LORDSn1per/OpenRemote-Hardware/PCB/Dock Rev6/Dock Rev6 3D Preview.png

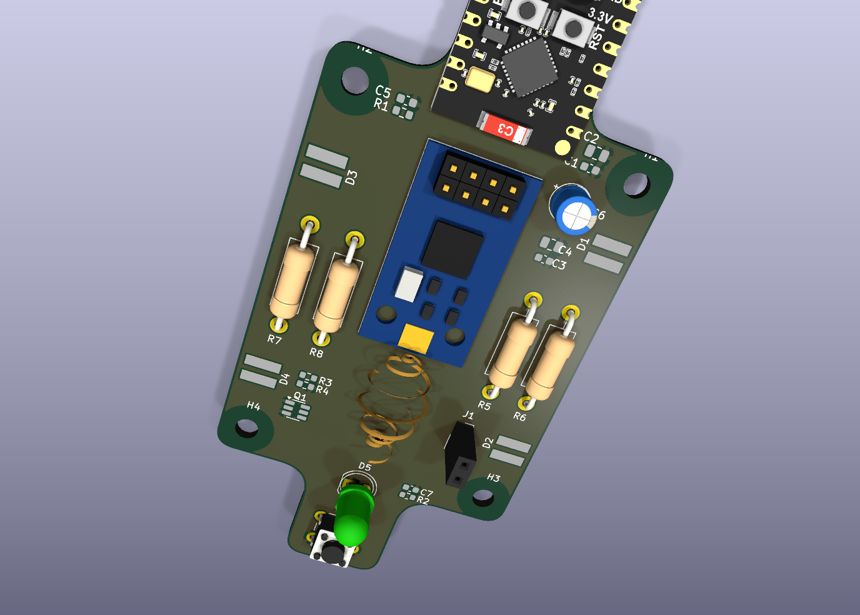
PCB/Dock Rev6/Dock Rev6 3D Preview.png
