LORDSn1per/OpenRemote-Hardware/CAD/Adafruit LCD/STL/Off Button Adafruit Rev6-v37.stl

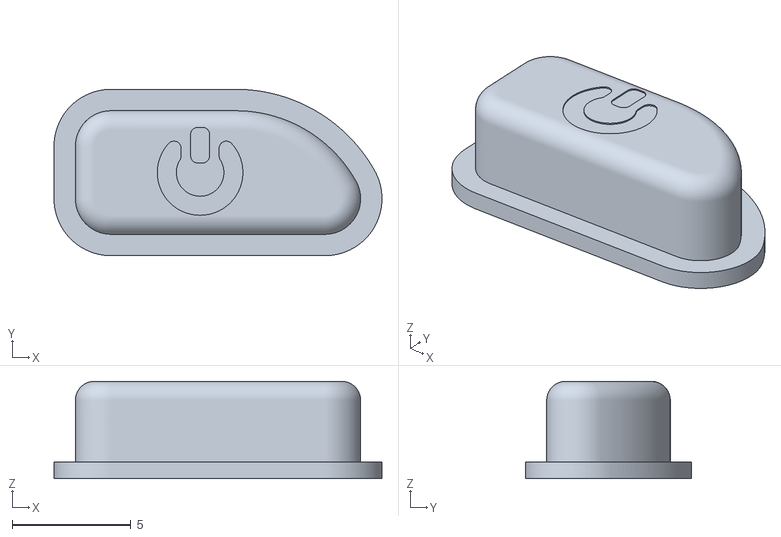
[picture p24: CAD file, 2026-09-03]
CAD/Adafruit LCD/STL/Off Button Adafruit Rev6-v37.stl
13.8 x 7.00 x 4.10
