LORDSn1per/OpenRemote-Hardware/CAD/BuyDisplay LCD/STL/Off Button BuyDisplay Rev6-v37.stl

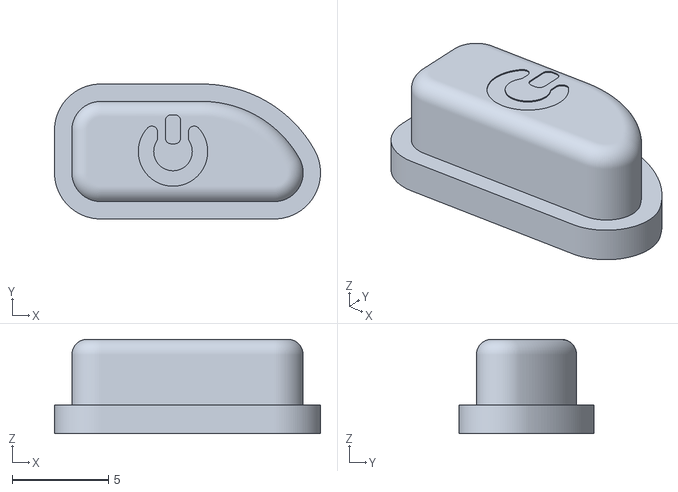
[picture p25: CAD file, 2026-09-03]
CAD/BuyDisplay LCD/STL/Off Button BuyDisplay Rev6-v37.stl
13.8 x 7.00 x 4.90
