LORDSn1per/OpenRemote-Hardware/CAD/Dock/STL/Dock Menu Button Rev6-v47.stl

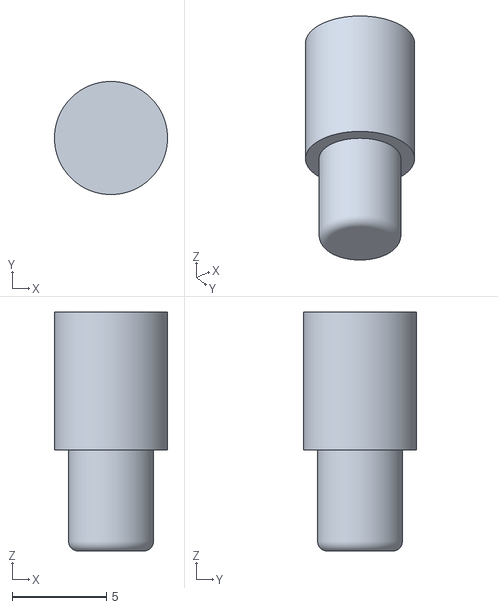
[picture p26: CAD file, 2026-09-03]
CAD/Dock/STL/Dock Menu Button Rev6-v47.stl
6.00 x 6.00 x 12.7
