LORDSn1per/OpenRemote-Hardware/PCB/Dock Rev6/project_libraries/3D-models/JST_Compatible_Female_1x02_P2.54mm.step

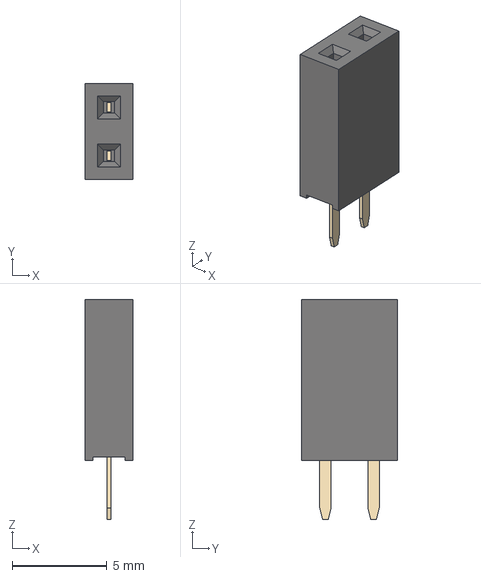
[picture p27: CAD file, 2026-08-27]
PCB/Dock Rev6/project_libraries/3D-models/JST_Compatible_Female_1x02_P2.54mm.step
2.54 x 5.08 x 11.6 mm
