LORDSn1per/OpenRemote-Hardware/PCB/Revision 6/project_libraries/3D-models/ER-TFT028-4.2_Folded.step

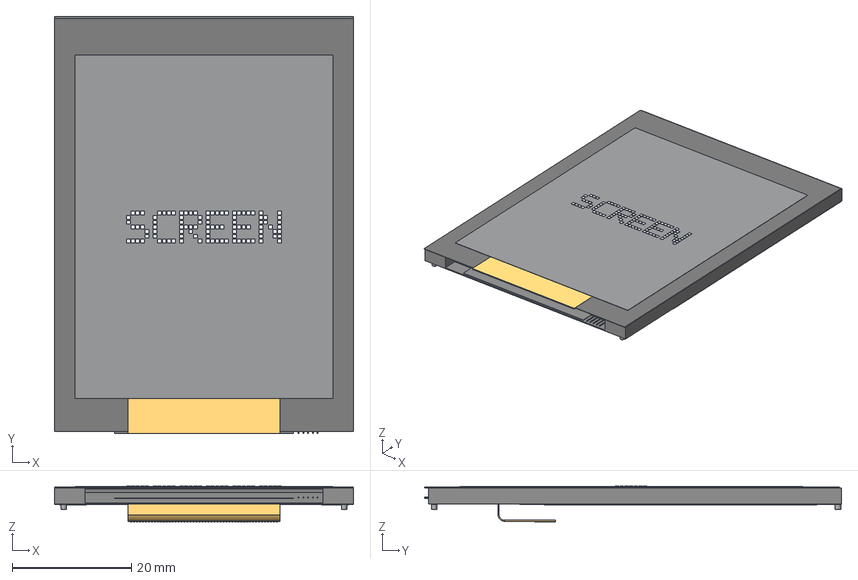
[picture p28: CAD file, 2026-08-07]
PCB/Revision 6/project_libraries/3D-models/ER-TFT028-4.2_Folded.step
50.2 x 69.9 x 5.99 mm
display_front_00_part
display_front_01_part
display_front_02_part
display_front_03_part
display_front_04_part
display_front_05_part
display_front_06_part
display_front_07_part
screen_label_0_0_1_part
screen_label_0_0_2_part
screen_label_0_0_3_part
screen_label_0_1_0_part
screen_label_0_2_0_part
screen_label_0_3_1_part
screen_label_0_3_2_part
screen_label_0_3_3_part
screen_label_0_4_4_part
screen_label_0_5_4_part
screen_label_0_6_0_part
screen_label_0_6_1_part
screen_label_0_6_2_part
screen_label_0_6_3_part
screen_label_1_0_1_part
screen_label_1_0_2_part
screen_label_1_0_3_part
screen_label_1_0_4_part
screen_label_1_1_0_part
screen_label_1_2_0_part
screen_label_1_3_0_part
screen_label_1_4_0_part
screen_label_1_5_0_part
screen_label_1_6_1_part
screen_label_1_6_2_part
screen_label_1_6_3_part
screen_label_1_6_4_part
screen_label_2_0_0_part
screen_label_2_0_1_part
screen_label_2_0_2_part
screen_label_2_0_3_part
screen_label_2_1_0_part
screen_label_2_1_4_part
screen_label_2_2_0_part
screen_label_2_2_4_part
screen_label_2_3_0_part
screen_label_2_3_1_part
screen_label_2_3_2_part
screen_label_2_3_3_part
screen_label_2_4_0_part
screen_label_2_4_2_part
screen_label_2_5_0_part
screen_label_2_5_3_part
screen_label_2_6_0_part
screen_label_2_6_4_part
screen_label_3_0_0_part
screen_label_3_0_1_part
screen_label_3_0_2_part
screen_label_3_0_3_part
screen_label_3_0_4_part
screen_label_3_1_0_part
screen_label_3_2_0_part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
