LORDSn1per/OpenRemote-Hardware/CAD/Adafruit LCD/STL/Colour Button Adafruit Rev6-v37.stl

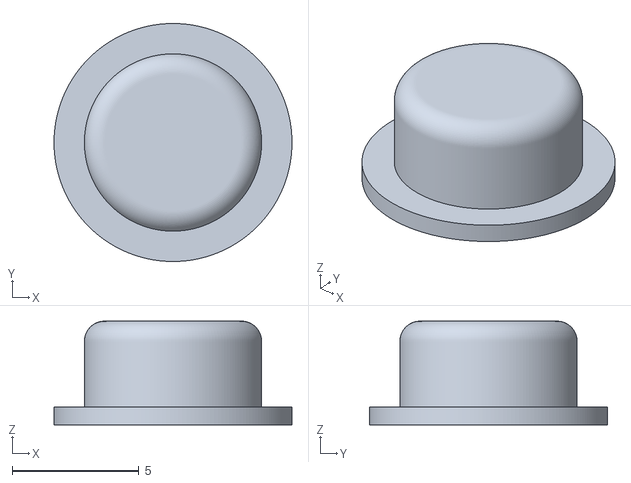
[picture p29: CAD file, 2026-09-03]
CAD/Adafruit LCD/STL/Colour Button Adafruit Rev6-v37.stl
9.40 x 9.40 x 4.10
