LORDSn1per/OpenRemote-Hardware/CAD/BuyDisplay LCD/STL/Cover Plate 5mm (+1mm) Rev6-v37.stl

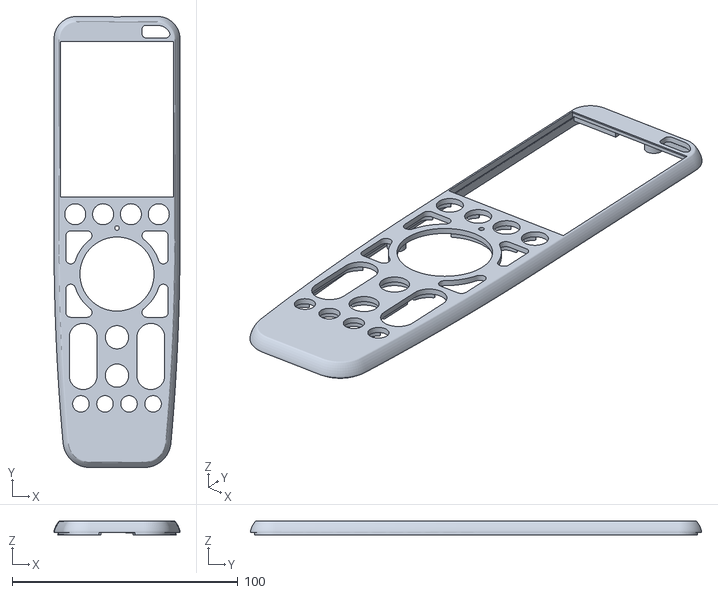
[picture p30: CAD file, 2026-09-03]
CAD/BuyDisplay LCD/STL/Cover Plate 5mm (+1mm) Rev6-v37.stl
55.8 x 199.8 x 6.20
