LORDSn1per/OpenRemote-Hardware/PCB/Dock Rev6/project_libraries/3D-models/SW_6x6x5H_THT.step

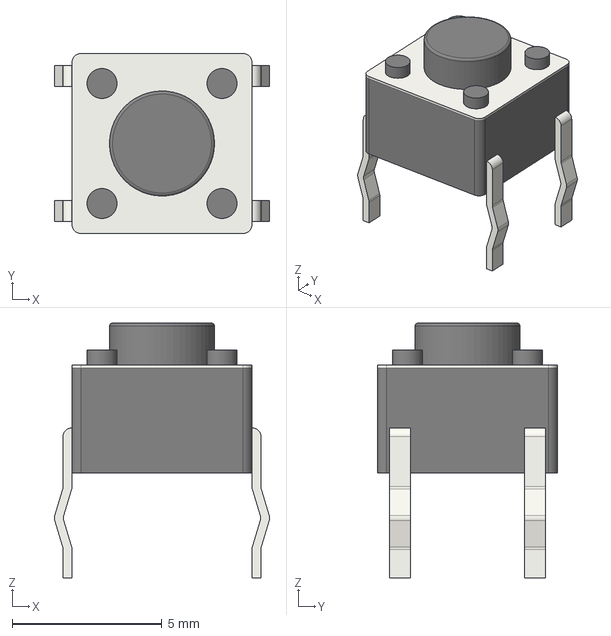
[picture p31: CAD file, 2026-08-27]
PCB/Dock Rev6/project_libraries/3D-models/SW_6x6x5H_THT.step
7.17 x 6.00 x 8.50 mm
