LORDSn1per/OpenRemote-Hardware/PCB/Revision 6/project_libraries/3D-models/MS3625_Circular_Microphone_Module_No_Headers.step

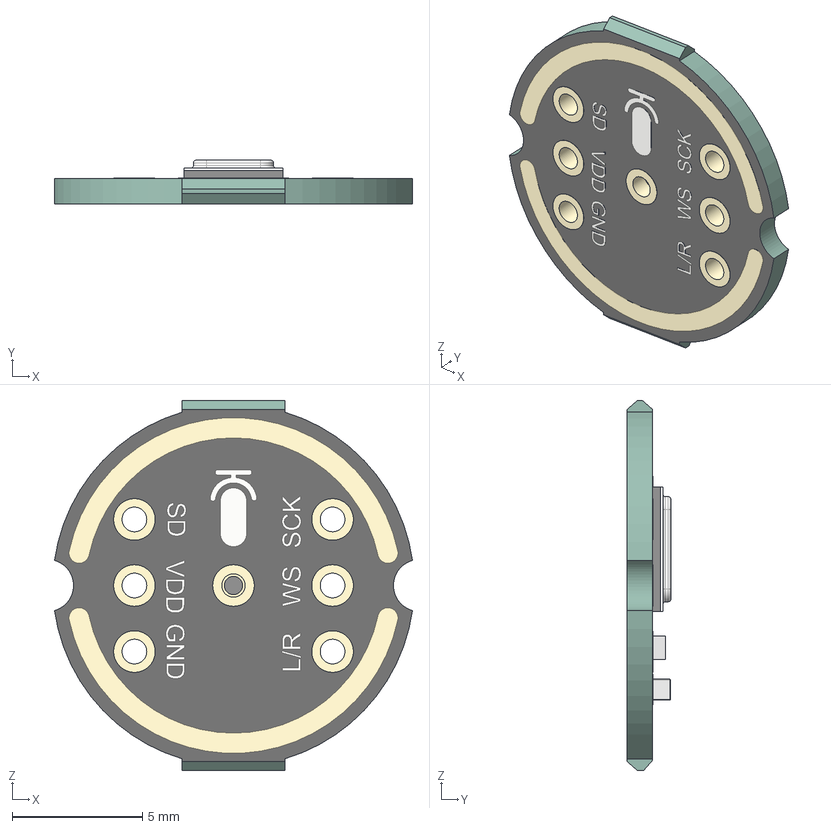
[picture p32: CAD file, 2026-08-04]
PCB/Revision 6/project_libraries/3D-models/MS3625_Circular_Microphone_Module_No_Headers.step
13.8 x 1.70 x 14.2 mm
0603 Resistor
