LORDSn1per/OpenRemote-Hardware/CAD/Adafruit LCD/STL/Cover Plate 4mm (+0mm) Rev6-v37.stl

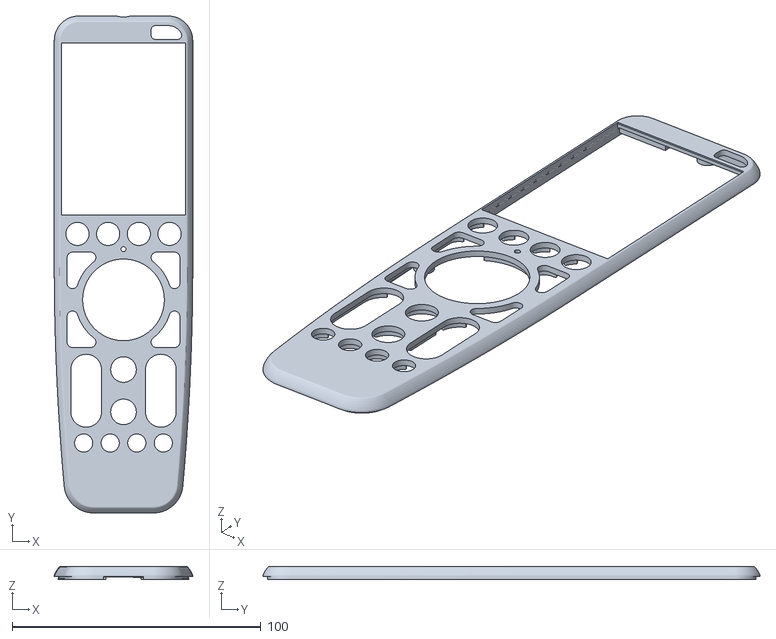
[picture p33: CAD file, 2026-09-03]
CAD/Adafruit LCD/STL/Cover Plate 4mm (+0mm) Rev6-v37.stl
55.7 x 199.7 x 5.20
