LORDSn1per/OpenRemote-Hardware/CAD/BuyDisplay LCD/STL/Button Grid BuyDisplay Rev6-v37.stl

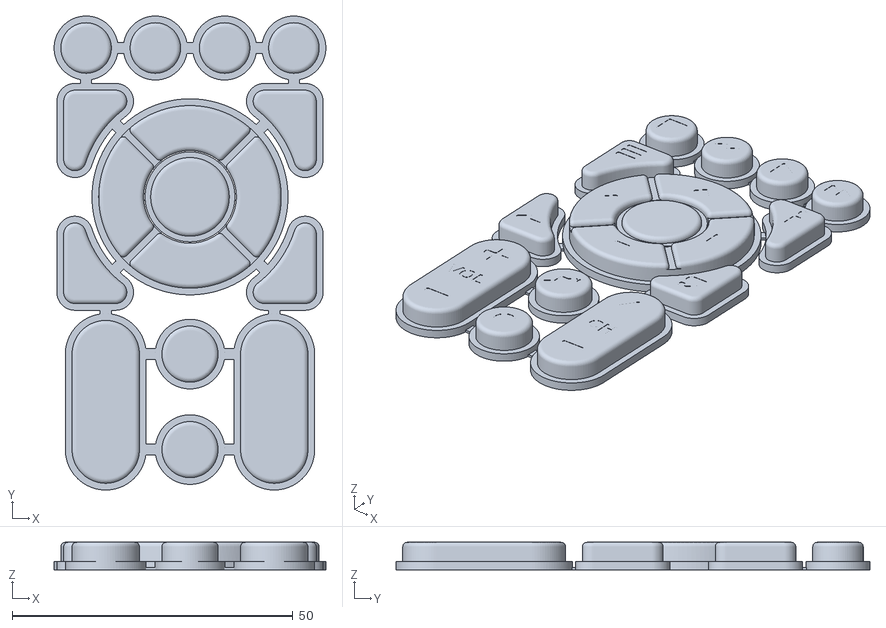
[picture p34: CAD file, 2026-09-03]
CAD/BuyDisplay LCD/STL/Button Grid BuyDisplay Rev6-v37.stl
48.4 x 84.4 x 4.90
