LORDSn1per/OpenRemote-Hardware/PCB/Dock Rev6/project_libraries/3D-models/ESP32-C3_SuperMini_2x08_Header.step

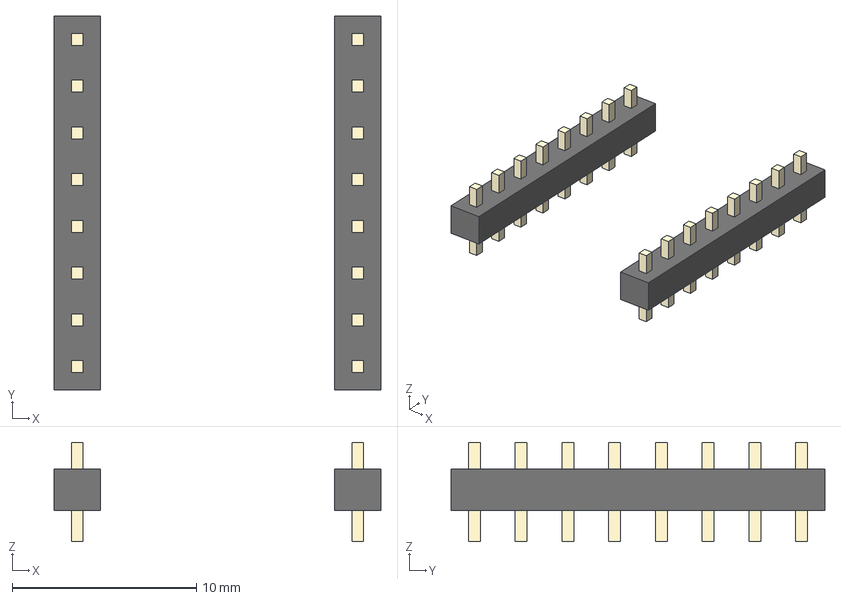
[picture p35: CAD file, 2026-08-27]
PCB/Dock Rev6/project_libraries/3D-models/ESP32-C3_SuperMini_2x08_Header.step
17.7 x 20.3 x 5.40 mm
