LORDSn1per/OpenRemote-Hardware/PCB/Revision 6/project_libraries/3D-models/B2B-PH-SM4-TB.STEP

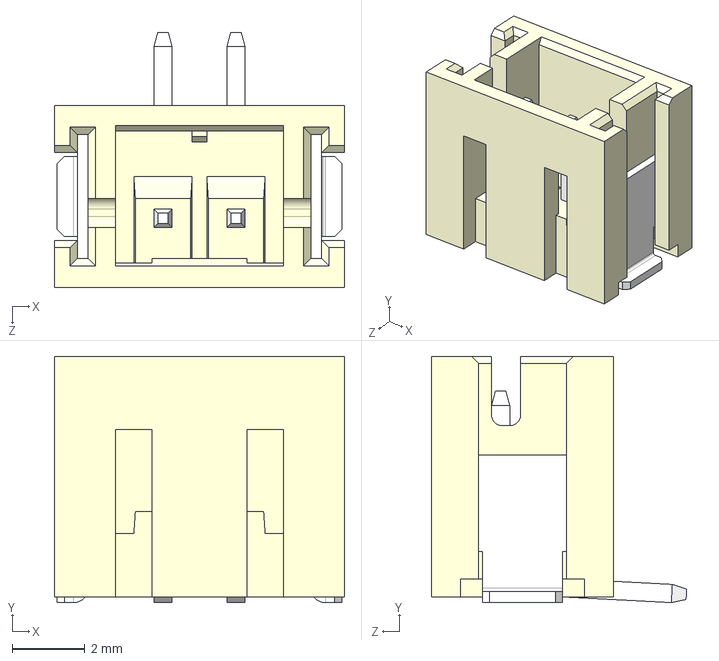
[picture p36: CAD file, 2026-08-04]
PCB/Revision 6/project_libraries/3D-models/B2B-PH-SM4-TB.STEP
7.95 x 6.75 x 7.00 mm
