LORDSn1per/OpenRemote-Hardware/CAD/Adafruit LCD/STL/Button Grid Adafruit Rev6-v37.stl

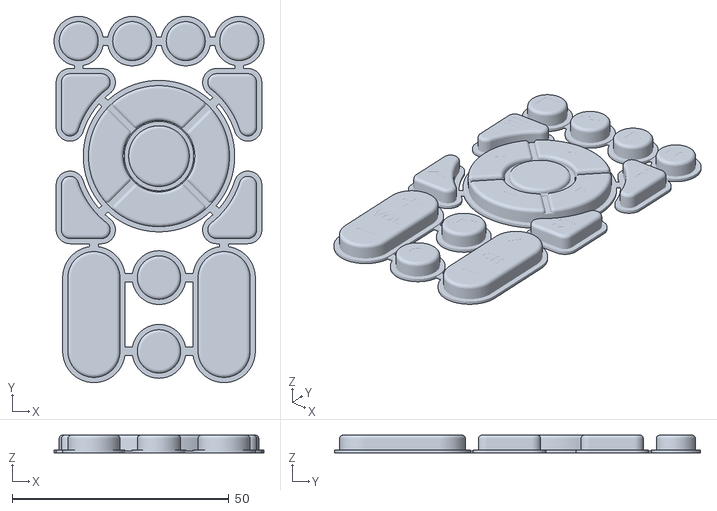
[picture p37: CAD file, 2026-09-03]
CAD/Adafruit LCD/STL/Button Grid Adafruit Rev6-v37.stl
48.4 x 84.4 x 4.10
