LORDSn1per/OpenRemote-Hardware/CAD/BuyDisplay LCD/STL/Colour Button BuyDisplay Rev6-v37.stl

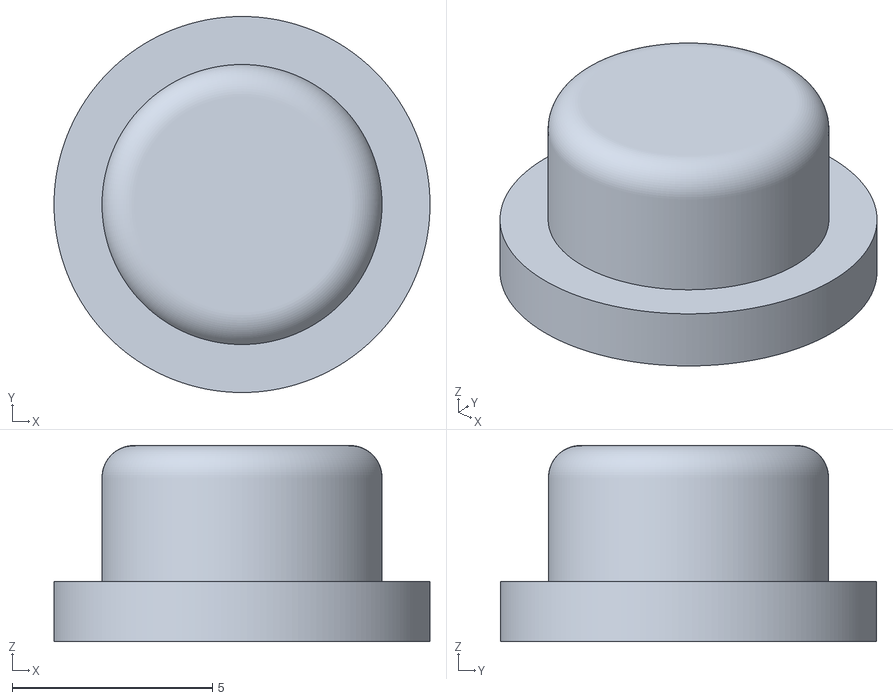
[picture p38: CAD file, 2026-09-03]
CAD/BuyDisplay LCD/STL/Colour Button BuyDisplay Rev6-v37.stl
9.40 x 9.40 x 4.90
