LORDSn1per/OpenRemote-Hardware/PCB/Dock Rev6/project_libraries/3D-models/CC1101_433MHz_Coil_Module.step

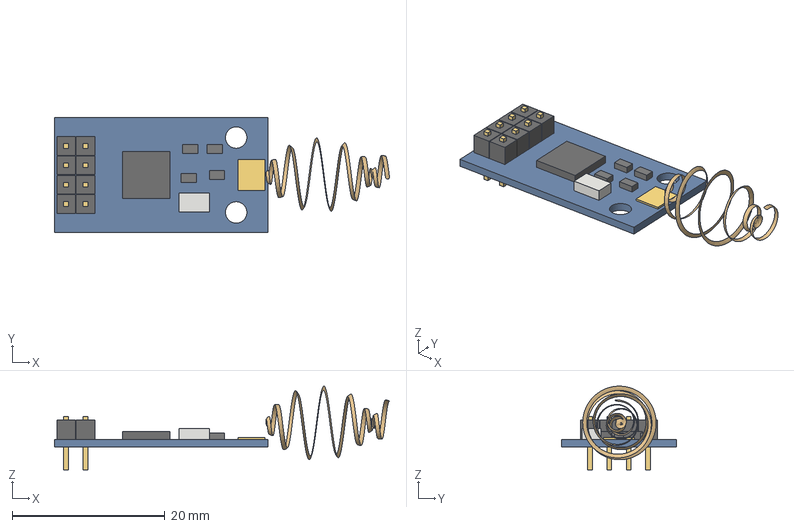
[picture p39: CAD file, 2026-08-27]
PCB/Dock Rev6/project_libraries/3D-models/CC1101_433MHz_Coil_Module.step
43.9 x 15.0 x 11.0 mm
PCB
CC1101
Crystal
RF component 0
RF component 1
RF component 2
RF component 3
Header pin 0 -1.27
Header body 0 -1.27
Header pin 0 1.27
Header body 0 1.27
Header pin 1 -1.27
Header body 1 -1.27
Header pin 1 1.27
Header body 1 1.27
Header pin 2 -1.27
Header body 2 -1.27
Header pin 2 1.27
Header body 2 1.27
Header pin 3 -1.27
Header body 3 -1.27
Header pin 3 1.27
Header body 3 1.27
Antenna pad
433MHz spring antenna
