LORDSn1per/OpenRemote-Hardware/PCB/Revision 6/project_libraries/3D-models/LIS3DHTR.step

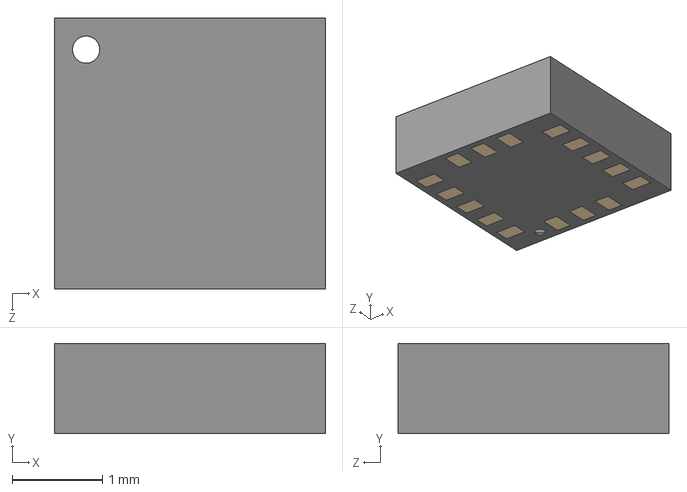
[picture p40: CAD file, 2026-08-04]
PCB/Revision 6/project_libraries/3D-models/LIS3DHTR.step
3.00 x 1.00 x 3.00 mm
