LORDSn1per/OpenRemote-Hardware/PCB/Dock Rev6/project_libraries/3D-models/ESP32-C3_SuperMini.step

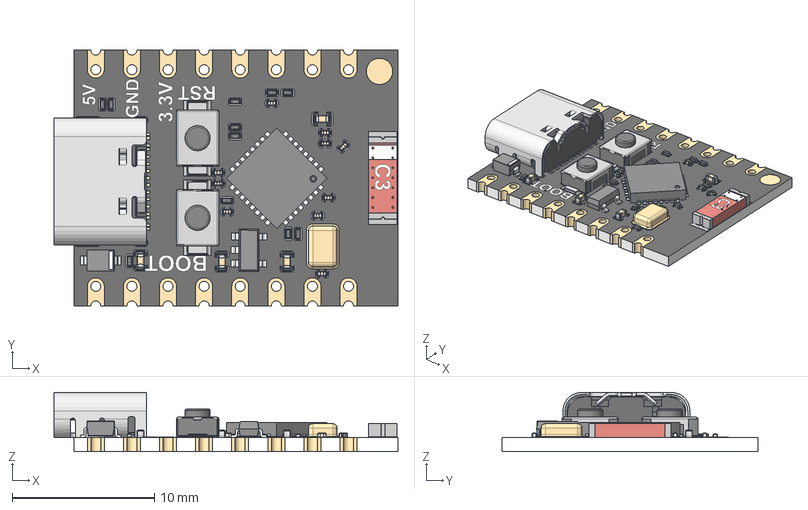
[picture p41: CAD file, 2026-08-27]
PCB/Dock Rev6/project_libraries/3D-models/ESP32-C3_SuperMini.step
24.2 x 18.0 x 4.16 mm
usb4215-03-a_1
RES0201 x 11
C0201 x 10
C0402 x 4
Cathode
Anode
Cathode Bar
Document
3x4x2mm - 2 button x 2
