LORDSn1per/OpenRemote-Hardware/PCB/Dock Rev6/project_libraries/3D-models/FS8205A_SOT-23-6.step

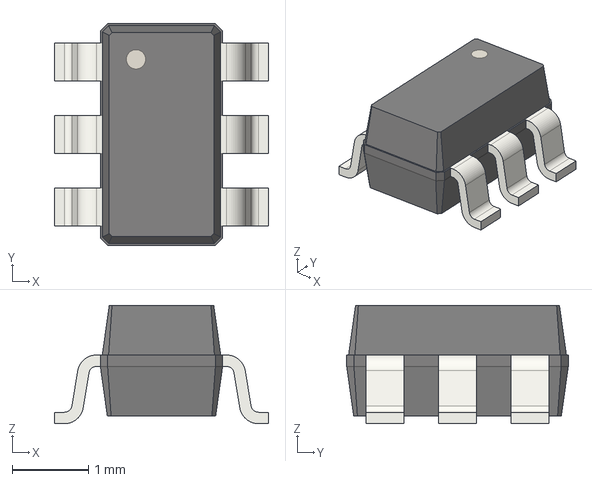
[picture p42: CAD file, 2026-08-27]
PCB/Dock Rev6/project_libraries/3D-models/FS8205A_SOT-23-6.step
2.80 x 2.90 x 1.55 mm
