LORDSn1per/OpenRemote-Hardware/PCB/Revision 6/project_libraries/3D-models/280QV10 v5.step

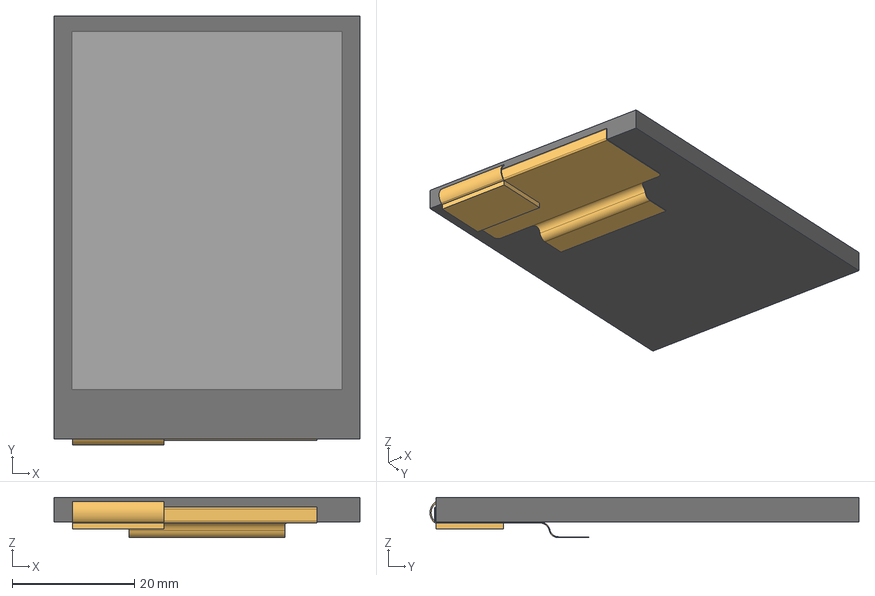
[picture p43: CAD file, 2026-08-04]
PCB/Revision 6/project_libraries/3D-models/280QV10 v5.step
50.0 x 70.2 x 6.60 mm
