LORDSn1per/OpenRemote-Hardware/PCB/Dock Rev6/project_libraries/3D-models/SW-TH_KH-6X6X5H-ZJ_C2837541.step

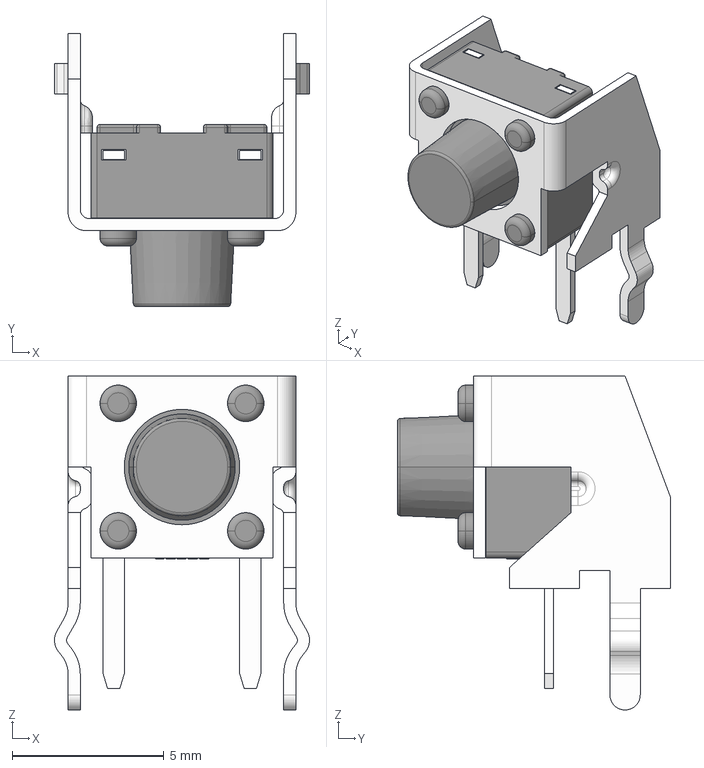
[picture p44: CAD file, 2026-08-27]
PCB/Dock Rev6/project_libraries/3D-models/SW-TH_KH-6X6X5H-ZJ_C2837541.step
8.40 x 9.00 x 11.0 mm
