LORDSn1per/OpenRemote-Hardware/PCB/Revision 6/project_libraries/3D-models/TF-01A.STEP

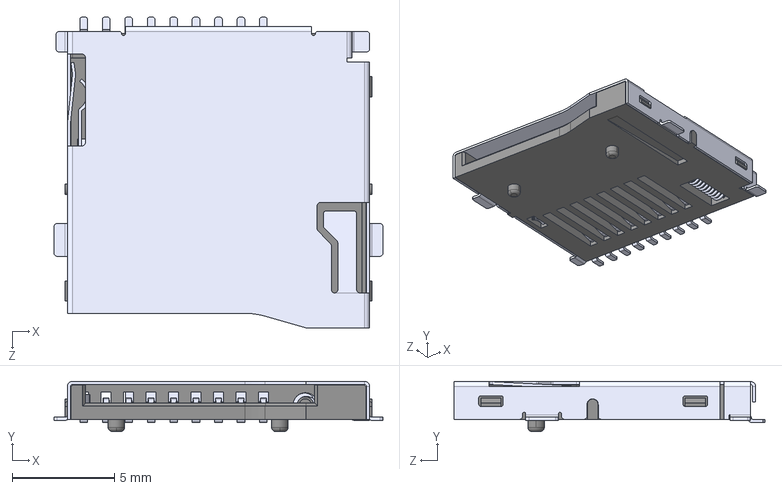
[picture p45: CAD file, 2026-08-04]
PCB/Revision 6/project_libraries/3D-models/TF-01A.STEP
16.1 x 2.45 x 15.2 mm
