LORDSn1per/OpenRemote-Hardware/PCB/Dock Rev6/project_libraries/3D-models/HX-XH2.54-2PZZ_C42391660.step

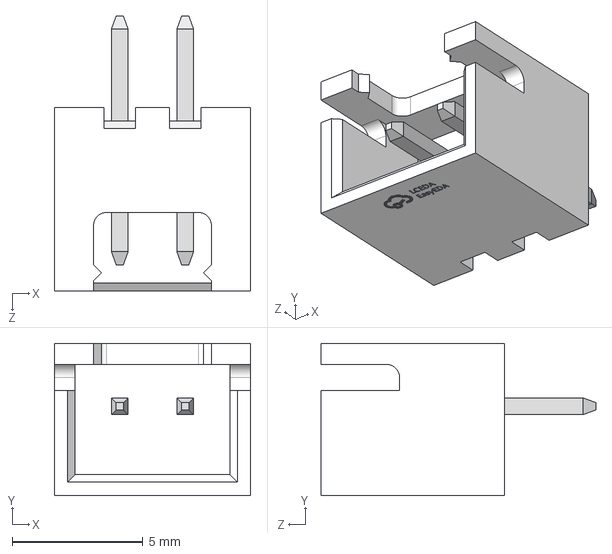
[picture p46: CAD file, 2026-08-27]
PCB/Dock Rev6/project_libraries/3D-models/HX-XH2.54-2PZZ_C42391660.step
7.50 x 5.81 x 10.5 mm
