LORDSn1per/OpenRemote-Hardware/PCB/Revision 6/project_libraries/3D-models/Walsin RFANT5220110A2T v1.step

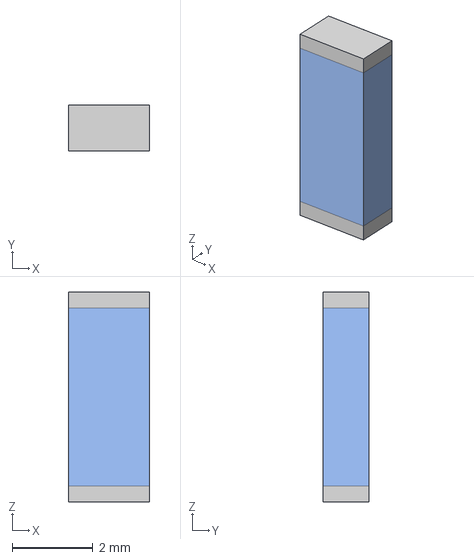
[picture p47: CAD file, 2026-08-04]
PCB/Revision 6/project_libraries/3D-models/Walsin RFANT5220110A2T v1.step
2.00 x 1.15 x 5.20 mm
