LORDSn1per/OpenRemote-Hardware/PCB/Dock Rev6/project_libraries/3D-models/Side Mount LED v1.step

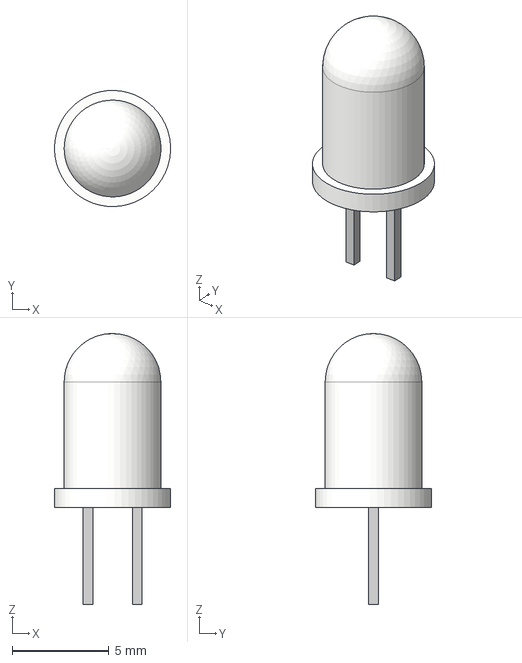
[picture p48: CAD file, 2026-08-04]
PCB/Dock Rev6/project_libraries/3D-models/Side Mount LED v1.step
5.99 x 6.00 x 14.0 mm
