LORDSn1per/OpenRemote-Hardware/PCB/Dock Rev6/Dock Rev6 PCB Assembly Preview Bottom.png

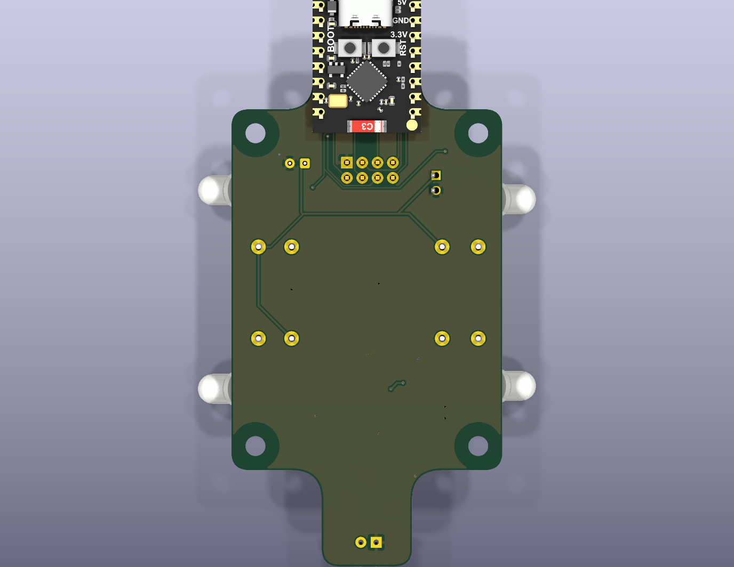
PCB/Dock Rev6/Dock Rev6 PCB Assembly Preview Bottom.png
